SolidHal/btrfld/demos/final_draft.gif

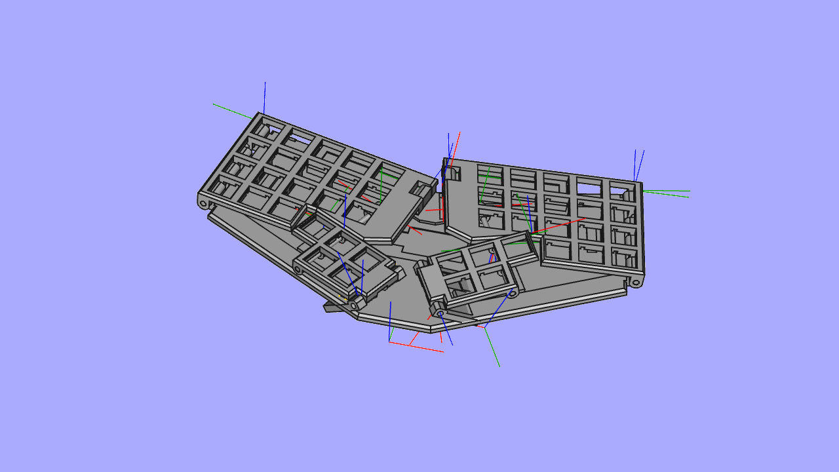
demos/final_draft.gif
