SolidHal/btrfld/demos/first_draft_demo_no_supports.gif

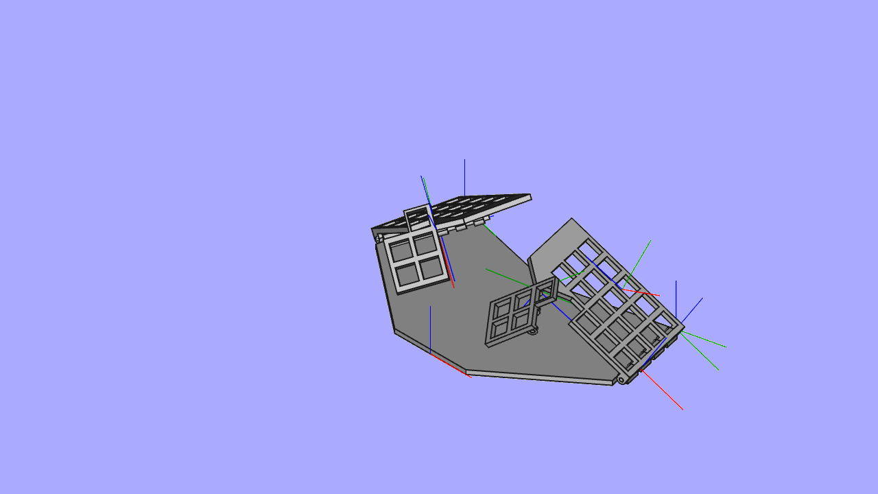
demos/first_draft_demo_no_supports.gif
