SolidHal/btrfld/FinishedPictures/btrfld_folded.jpeg

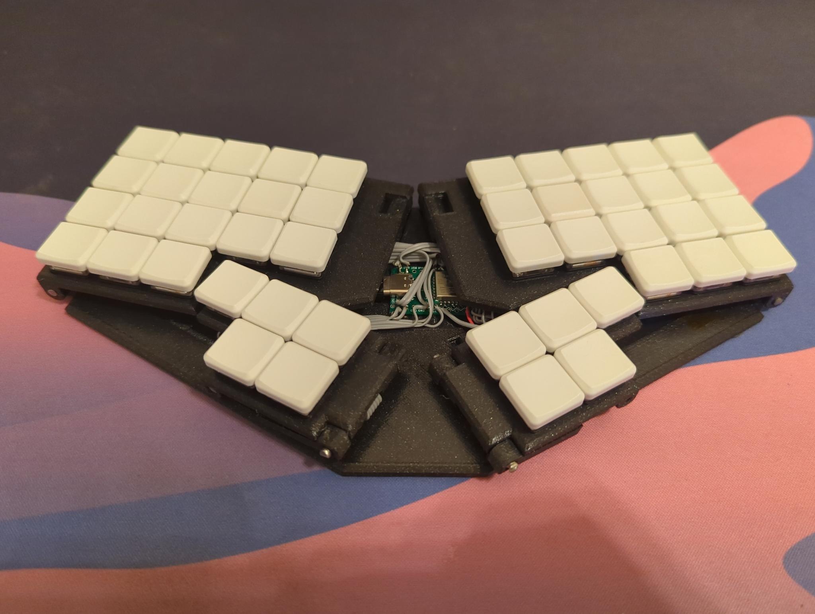
FinishedPictures/btrfld_folded.jpeg
