SolidHal/btrfld/FinishedPictures/btrfld_folded_thickness.jpeg

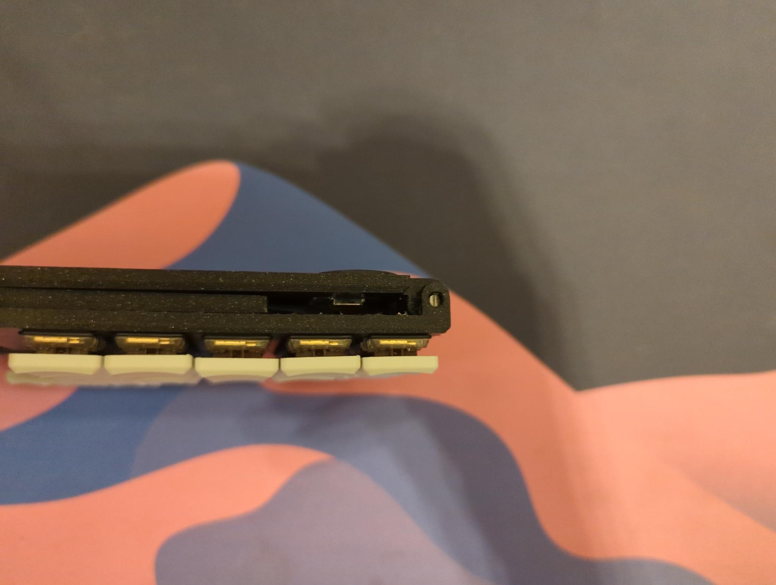
FinishedPictures/btrfld_folded_thickness.jpeg
