SolidHal/btrfld/FinishedPictures/btrfld_front_angle.jpeg

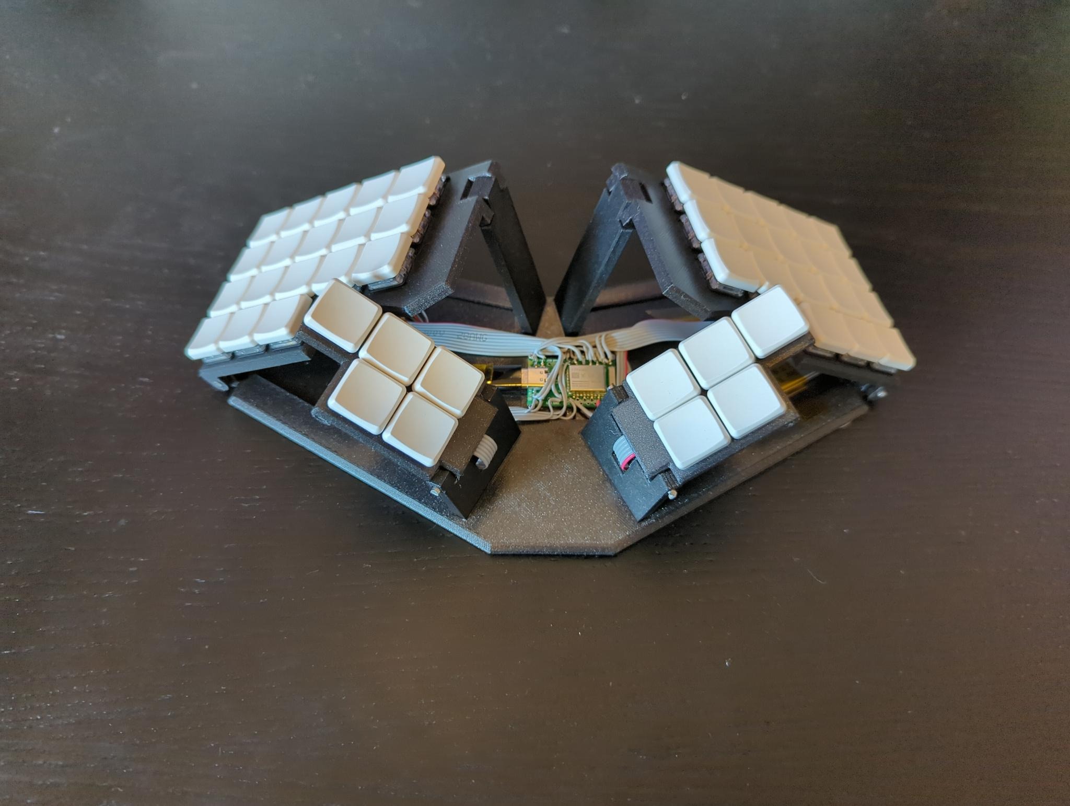
FinishedPictures/btrfld_front_angle.jpeg
