SolidHal/btrfld/FinishedPictures/btrfld_left_front.jpeg

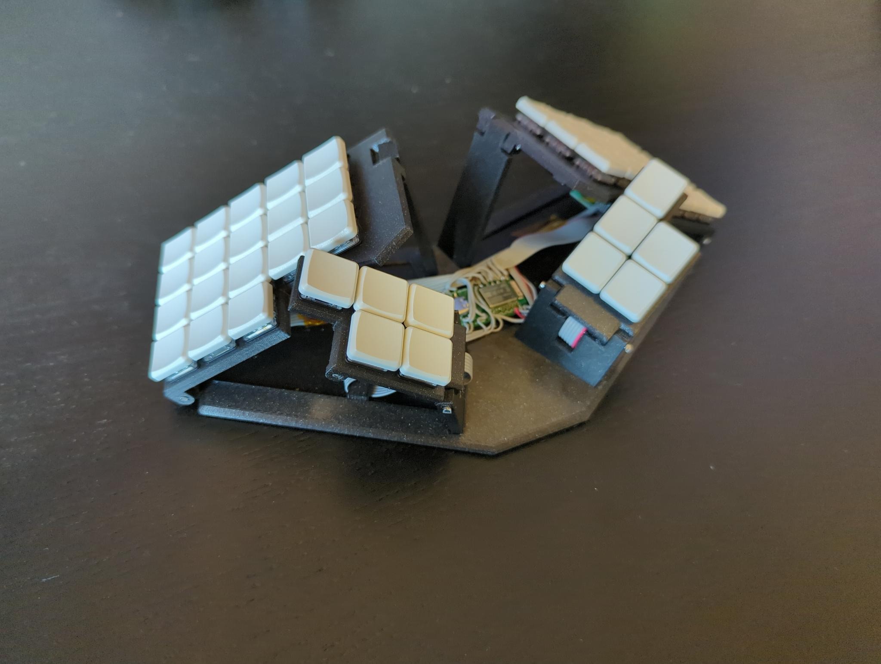
FinishedPictures/btrfld_left_front.jpeg
