SolidHal/btrfld/FinishedPictures/btrfld_right_front.jpeg

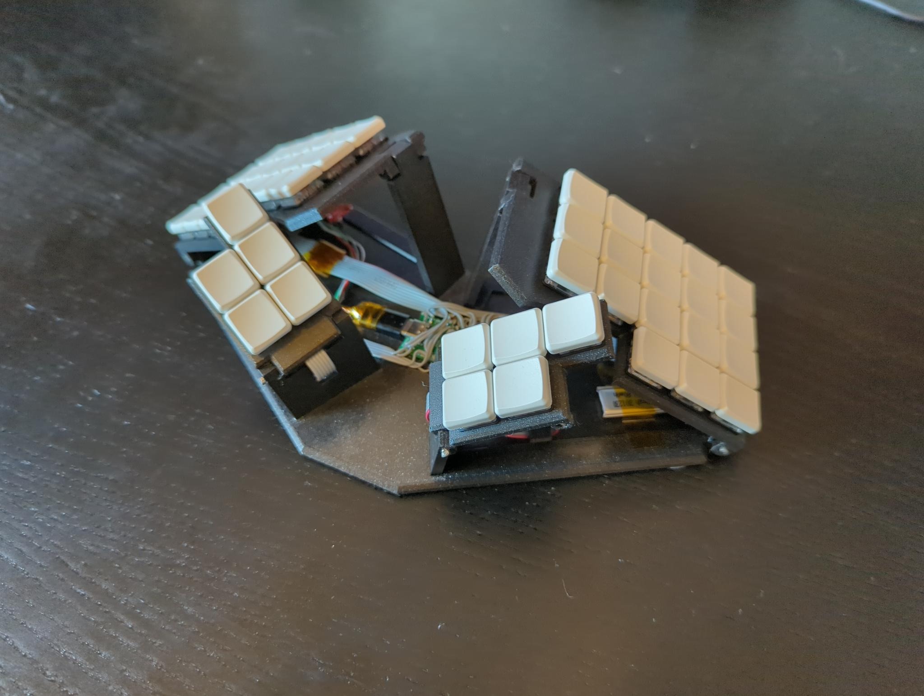
FinishedPictures/btrfld_right_front.jpeg
