SolidHal/btrfld/FinishedPictures/btrfld_top.jpeg

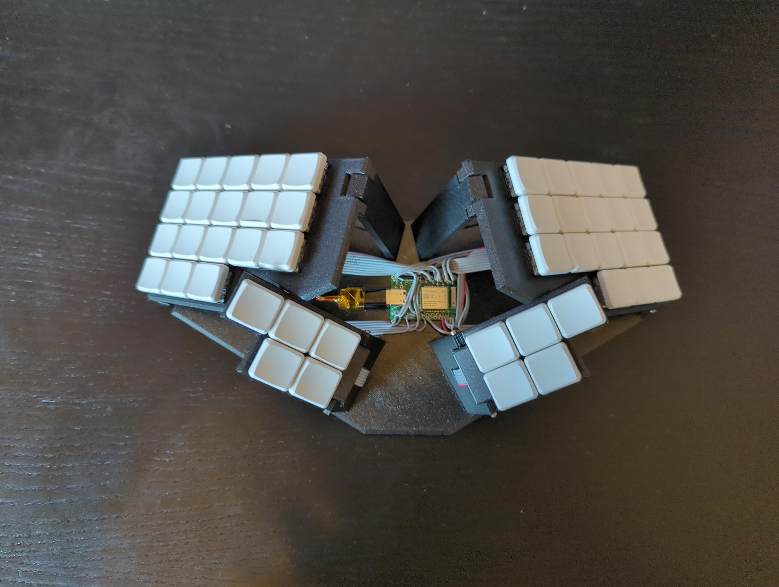
FinishedPictures/btrfld_top.jpeg
