SolidHal/btrfld/FinishedPictures/btrfld_with_btrfly/btrfld_btrfly_front.jpeg

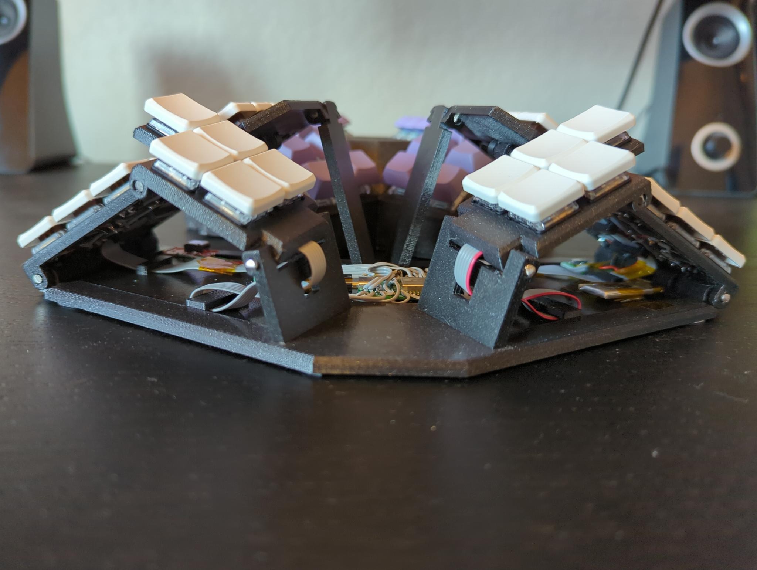
FinishedPictures/btrfld_with_btrfly/btrfld_btrfly_front.jpeg
