SolidHal/btrfld/FinishedPictures/btrfld_with_btrfly/btrfld_btrfly_front_left.jpeg

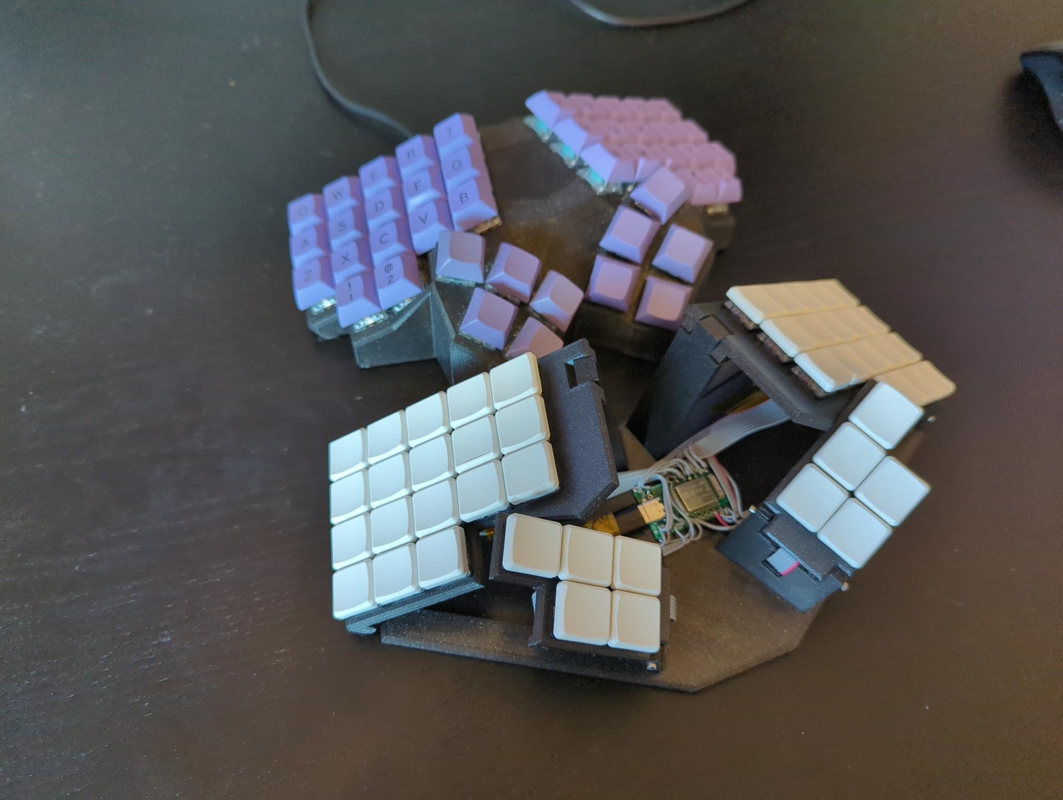
FinishedPictures/btrfld_with_btrfly/btrfld_btrfly_front_left.jpeg
