SolidHal/btrfld/FinishedPictures/btrfld_with_btrfly/btrfld_btrfly_front_top.jpeg

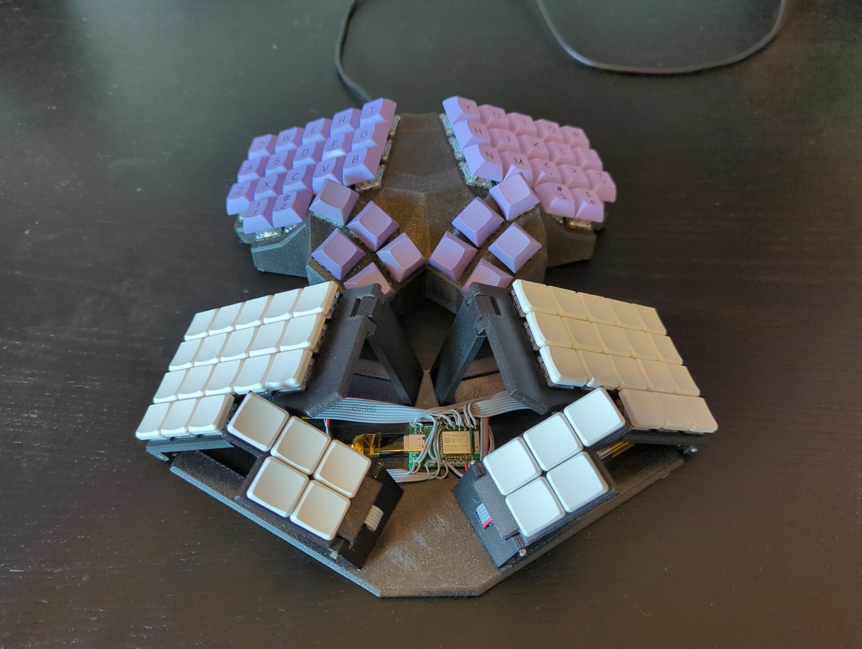
FinishedPictures/btrfld_with_btrfly/btrfld_btrfly_front_top.jpeg
