SolidHal/btrfld/FinishedPictures/btrfld_with_btrfly/btrfld_btrfly_top.jpeg

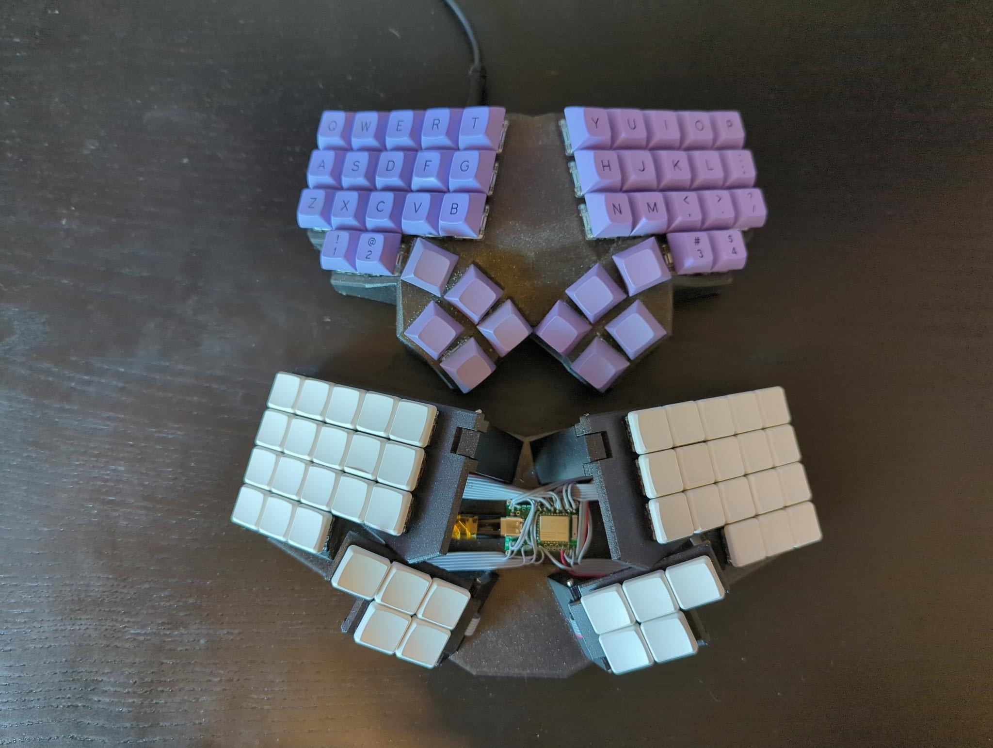
FinishedPictures/btrfld_with_btrfly/btrfld_btrfly_top.jpeg
