SolidHal/btrfld/FinishedPictures/btrfld_with_btrfly/pcb_handwired_btrfly_front_top.jpg

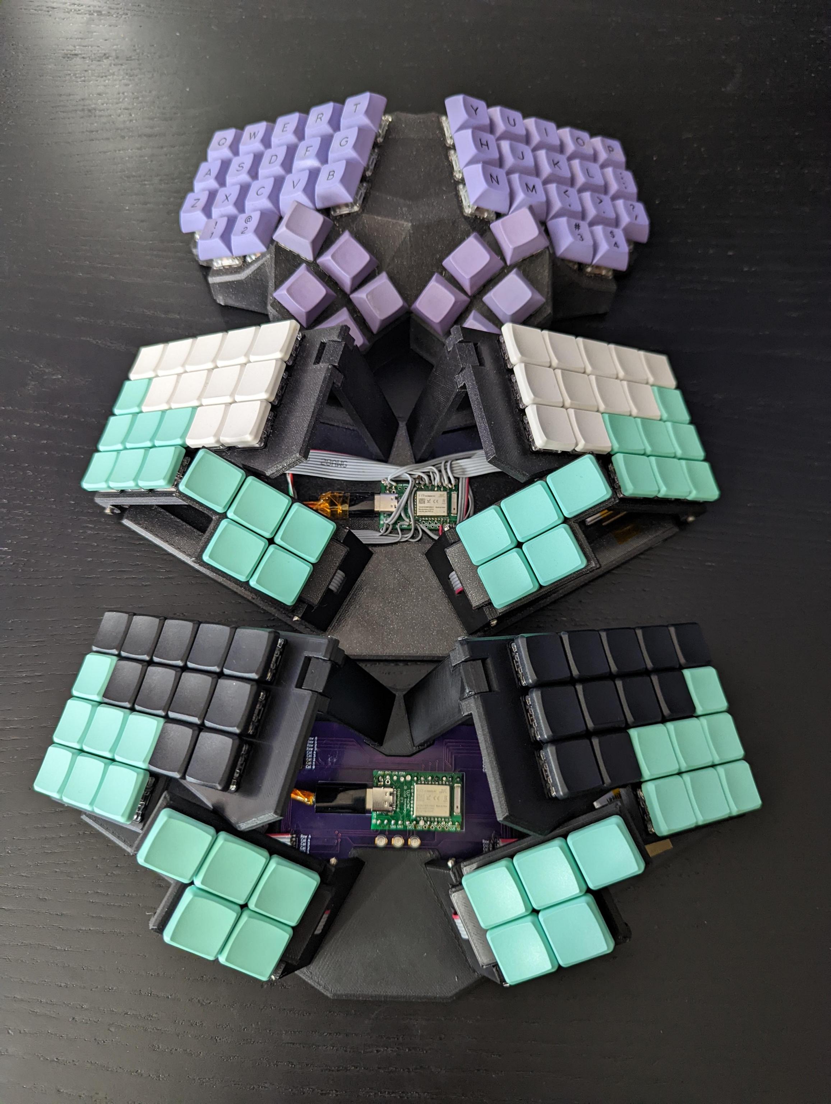
FinishedPictures/btrfld_with_btrfly/pcb_handwired_btrfly_front_top.jpg
