SolidHal/btrfld/FinishedPictures/pcb_handwired_hand_underside.jpg

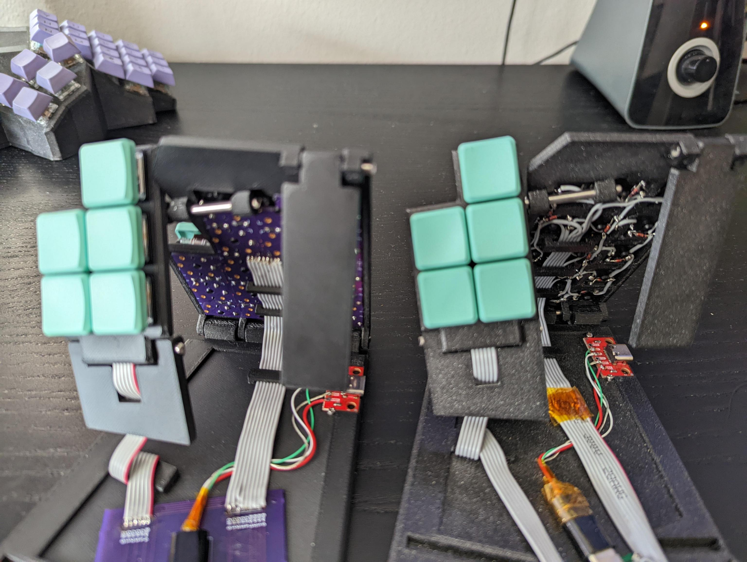
FinishedPictures/pcb_handwired_hand_underside.jpg
