SolidHal/btrfld/FinishedPictures/pcb_handwired_thumb_underside.jpg

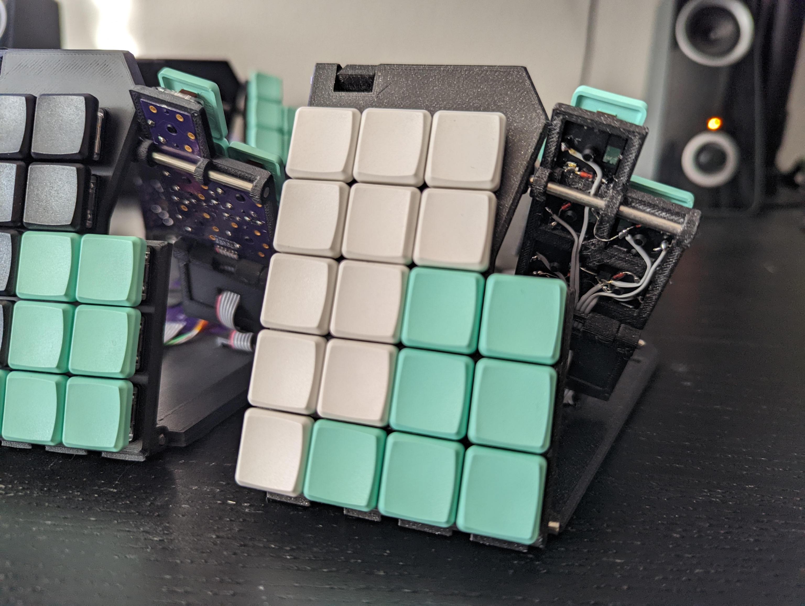
FinishedPictures/pcb_handwired_thumb_underside.jpg
