SolidHal/btrfld/FinishedPictures/ulp_head_on.jpeg

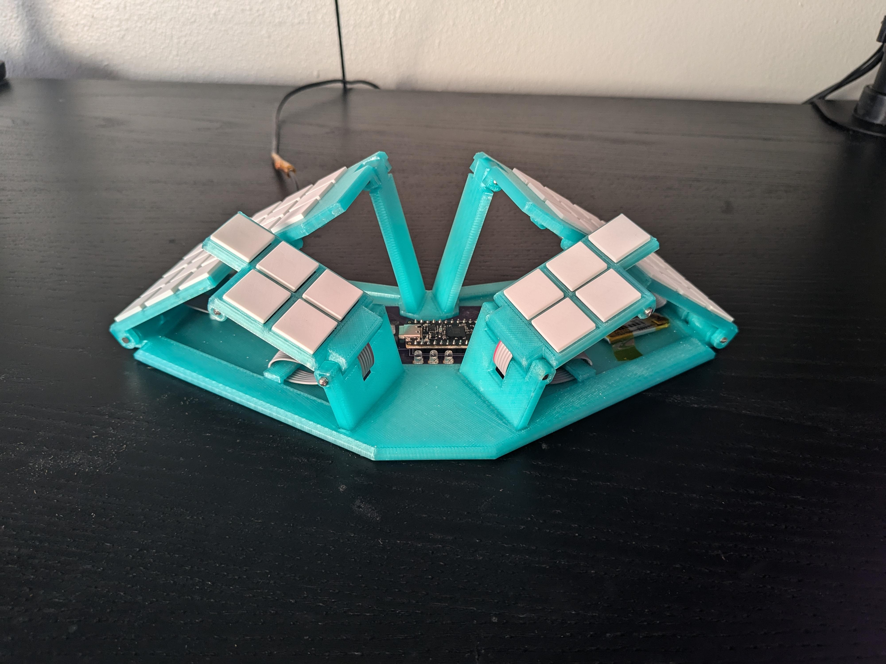
FinishedPictures/ulp_head_on.jpeg
