SolidHal/btrfld/FinishedPictures/ulp_side1.jpeg

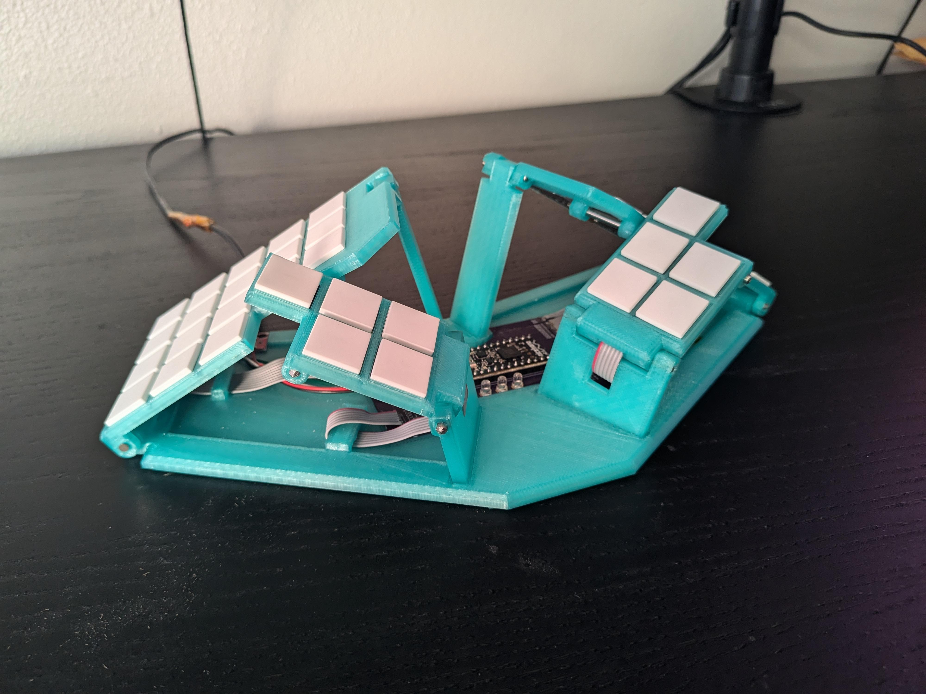
FinishedPictures/ulp_side1.jpeg
