SolidHal/btrfld/FinishedPictures/ulp_side2.jpeg

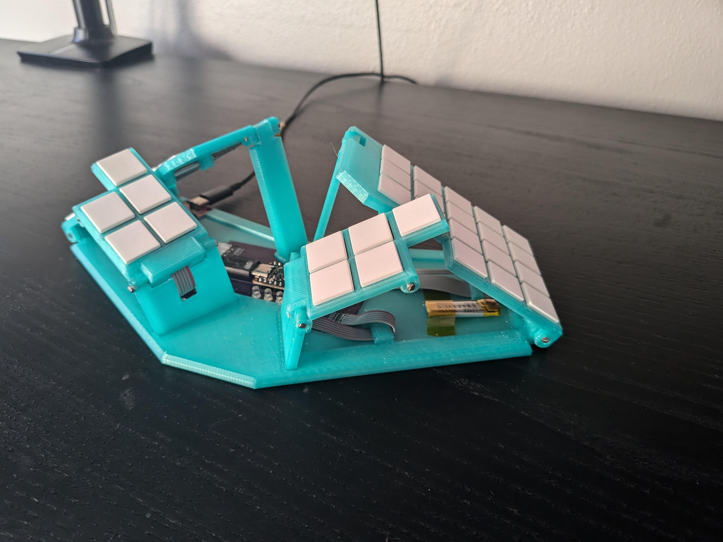
FinishedPictures/ulp_side2.jpeg
