SolidHal/btrfld/FinishedPictures/ulp_with_choc.jpeg

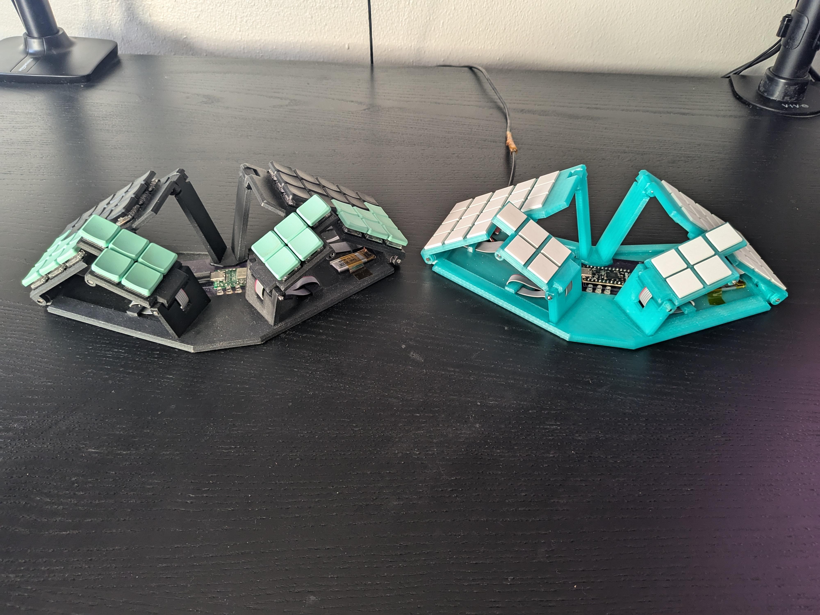
FinishedPictures/ulp_with_choc.jpeg
