SolidHal/btrfld/STLs/btrfld_pcb/test_fit-Baseplate.stl

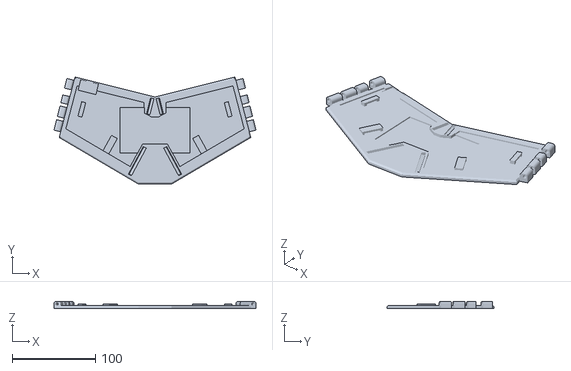
[picture p43: CAD file, 2023-01-31]
STLs/btrfld_pcb/test_fit-Baseplate.stl
242.4 x 128.3 x 9.00
