SolidHal/btrfld/STLs/btrfld_pcb/test_fit-BodyThumRodCap.stl

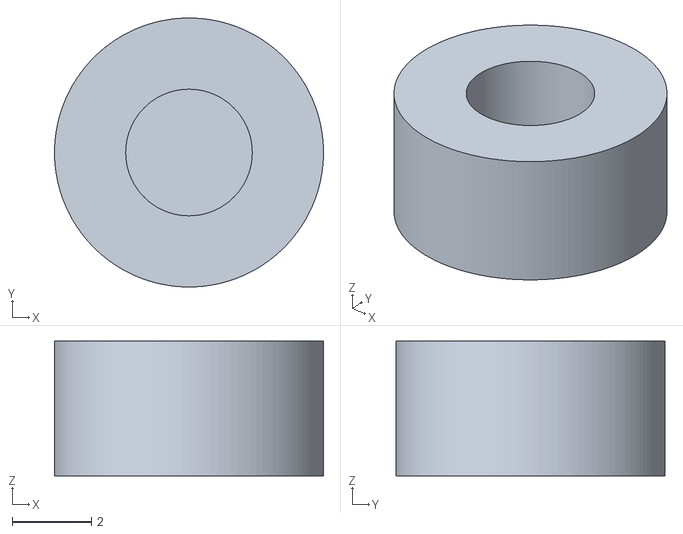
[picture p44: CAD file, 2022-04-27]
STLs/btrfld_pcb/test_fit-BodyThumRodCap.stl
6.80 x 6.80 x 3.40
