SolidHal/btrfld/STLs/btrfld_ulp/btrfld_ulp-BodyBaseSupportRight.stl

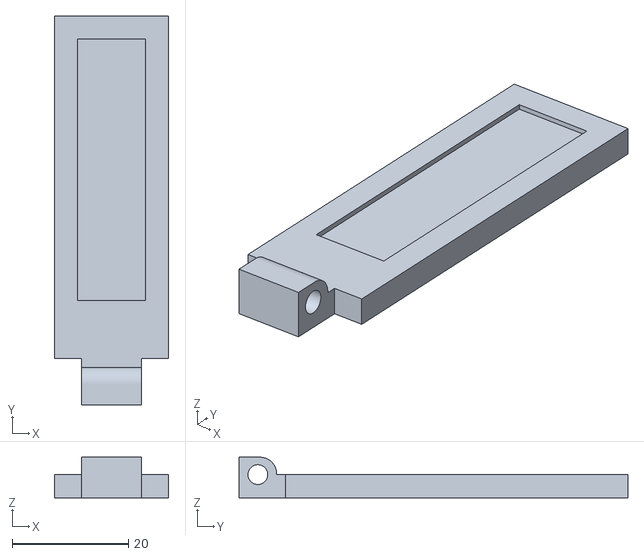
[picture p45: CAD file, 2022-04-27]
STLs/btrfld_ulp/btrfld_ulp-BodyBaseSupportRight.stl
19.7 x 67.0 x 7.00
