SolidHal/btrfld/BuildPictures/HANDWIRED/AllWired/LeftHandWired.jpeg

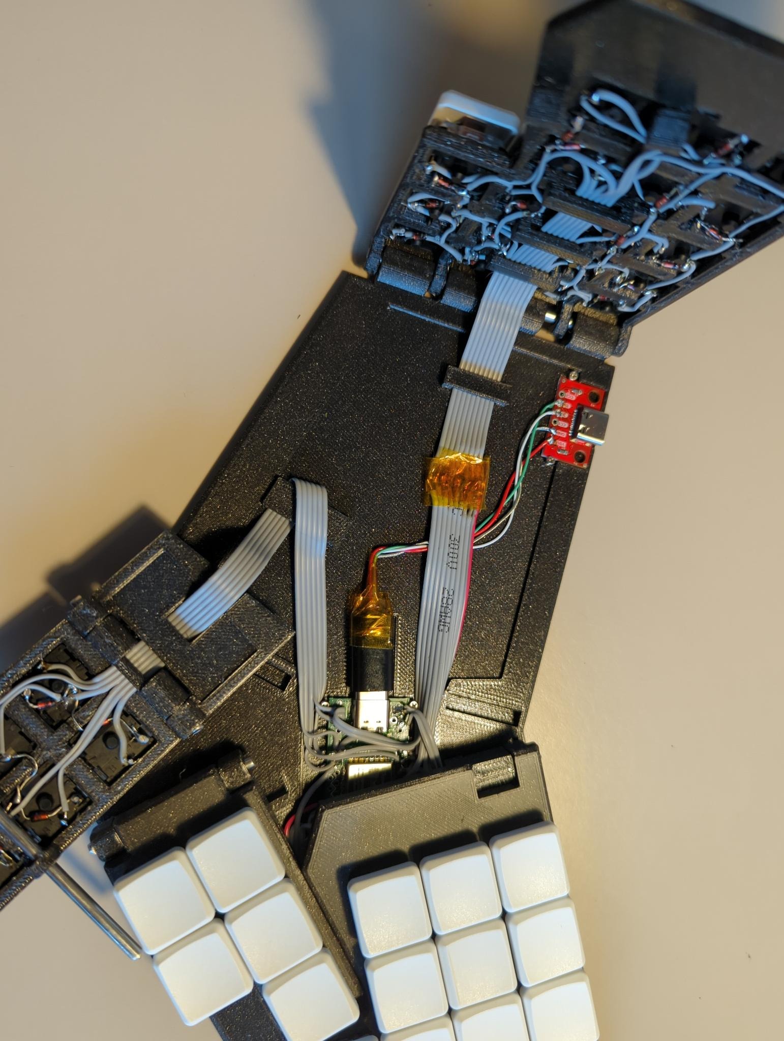
BuildPictures/HANDWIRED/AllWired/LeftHandWired.jpeg
