SolidHal/btrfld/BuildPictures/HANDWIRED/AllWired/LeftSide.jpeg

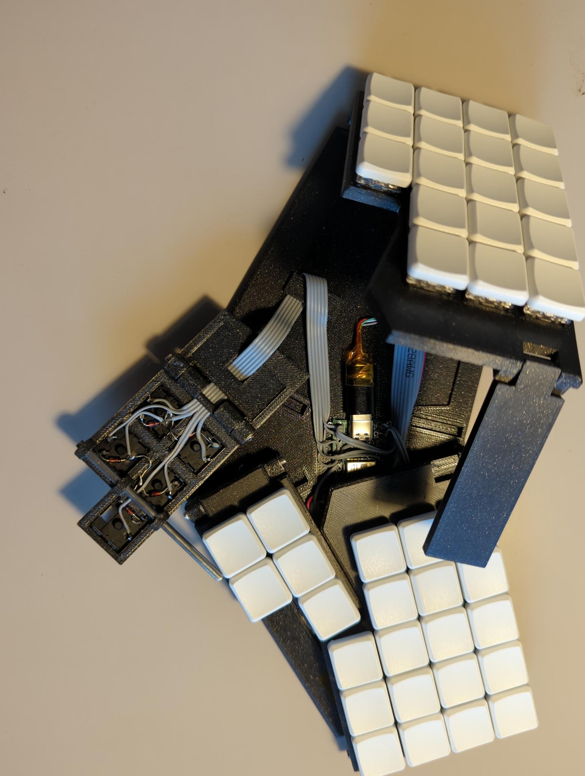
BuildPictures/HANDWIRED/AllWired/LeftSide.jpeg
