SolidHal/btrfld/BuildPictures/HANDWIRED/AllWired/LeftThumbWired.jpeg

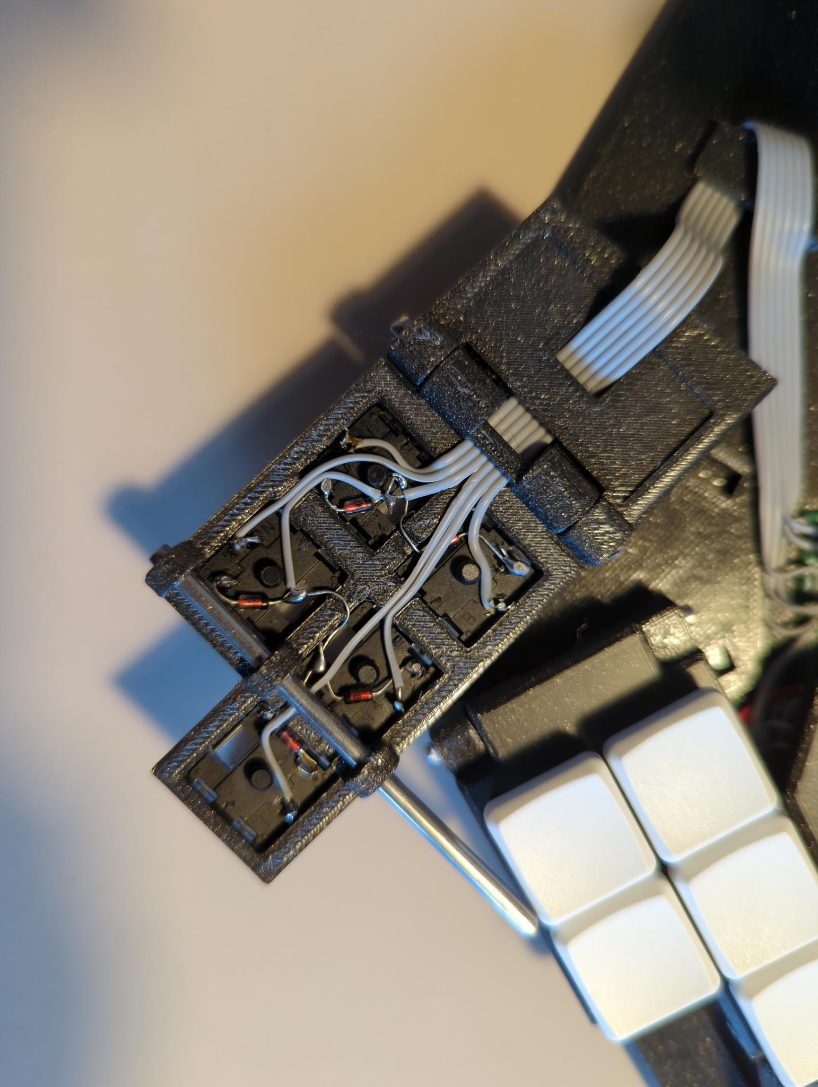
BuildPictures/HANDWIRED/AllWired/LeftThumbWired.jpeg
