SolidHal/btrfld/BuildPictures/HANDWIRED/AllWired/RightHandWiredUnderside.jpeg

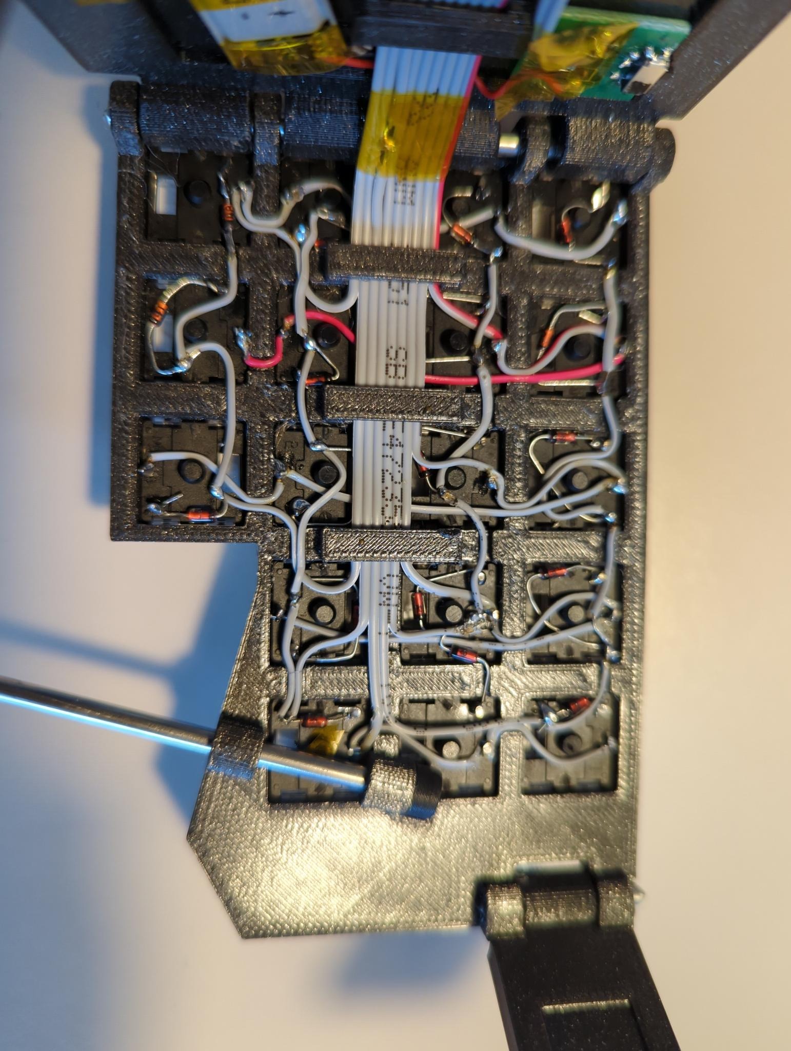
BuildPictures/HANDWIRED/AllWired/RightHandWiredUnderside.jpeg
