SolidHal/btrfld/BuildPictures/HANDWIRED/AllWired/RightSide2.jpeg

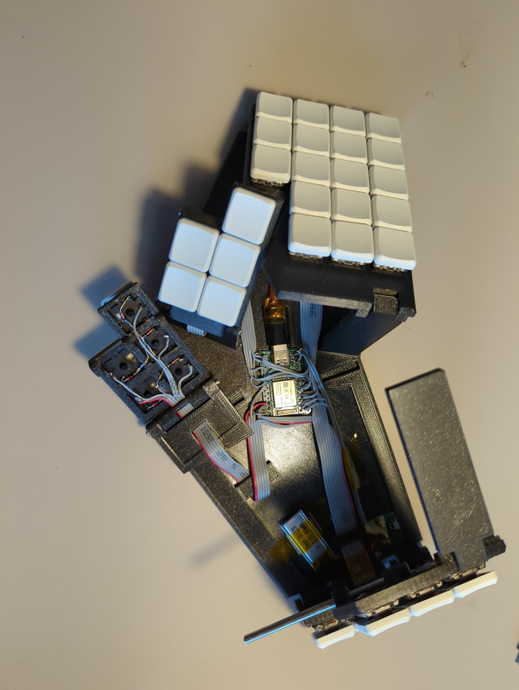
BuildPictures/HANDWIRED/AllWired/RightSide2.jpeg
