SolidHal/btrfld/BuildPictures/HANDWIRED/Assembly/left_hand_unwired.jpeg

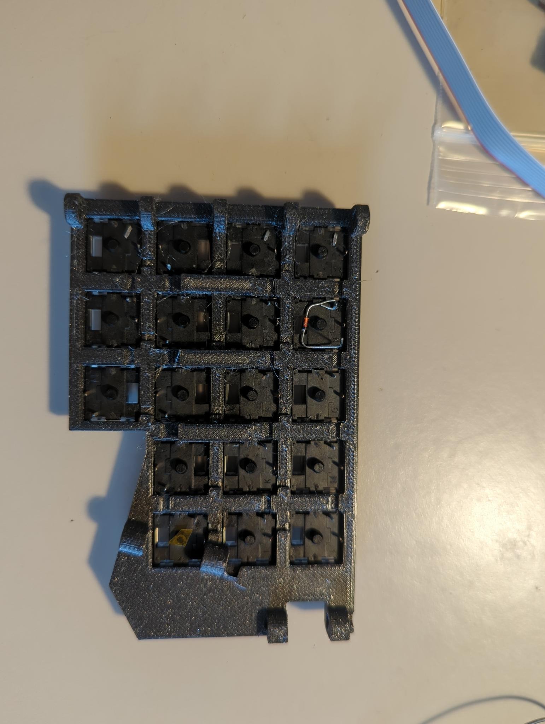
BuildPictures/HANDWIRED/Assembly/left_hand_unwired.jpeg
