SolidHal/btrfld/BuildPictures/HANDWIRED/Assembly/right_hand_wire_planning.jpeg

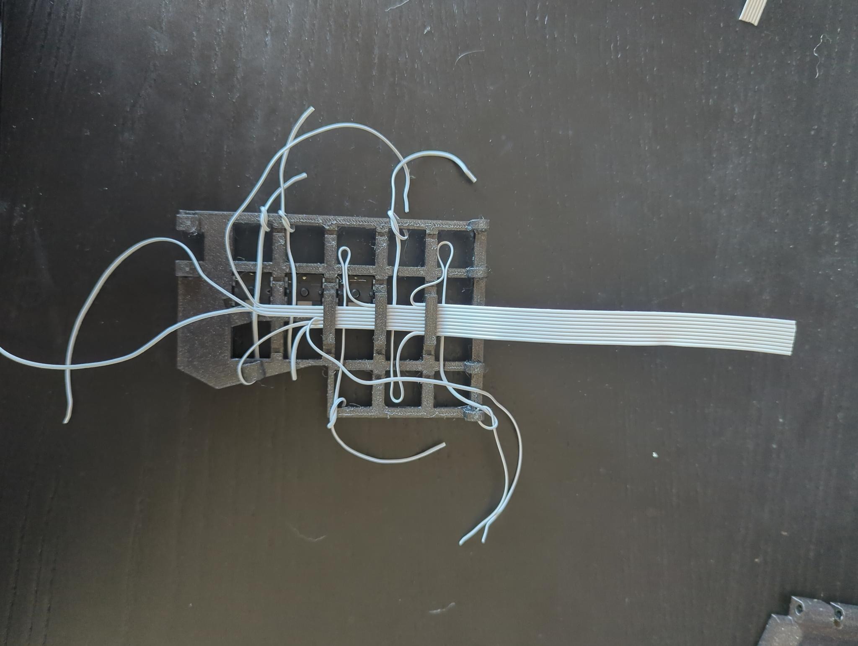
BuildPictures/HANDWIRED/Assembly/right_hand_wire_planning.jpeg
