SolidHal/btrfld/BuildPictures/HANDWIRED/Assembly/thumb_wired.jpeg

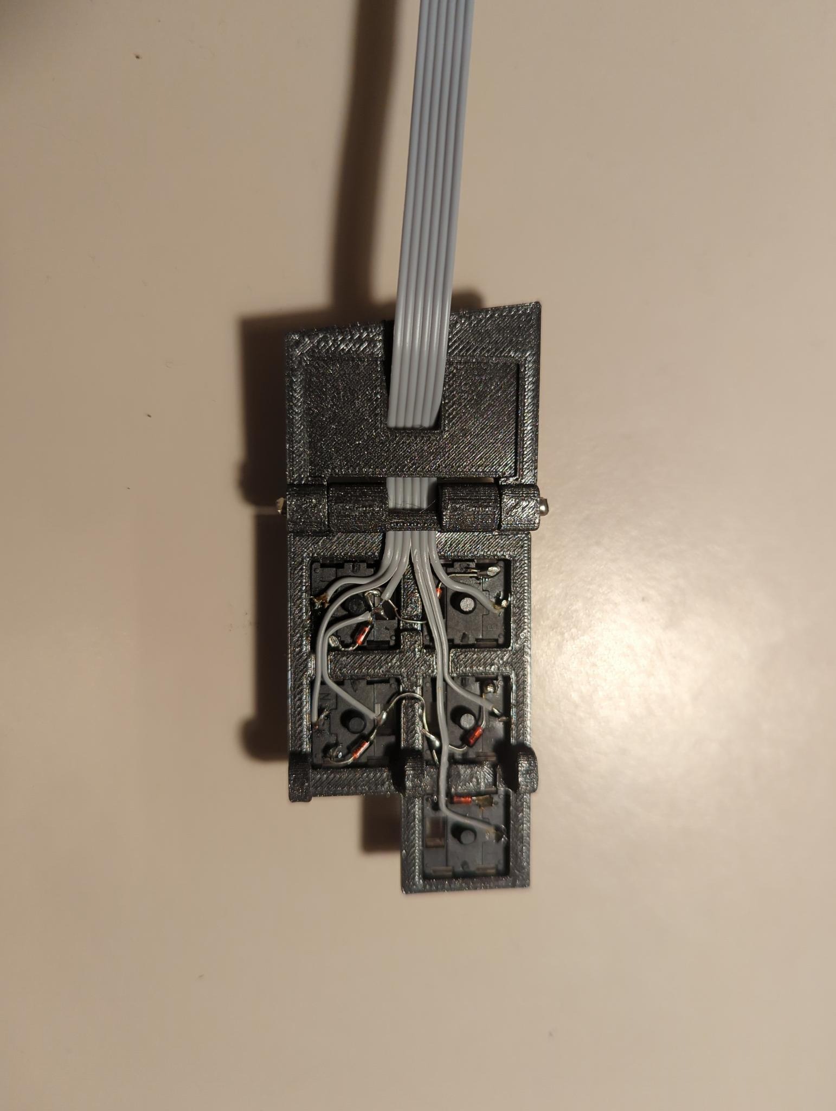
BuildPictures/HANDWIRED/Assembly/thumb_wired.jpeg
