SolidHal/btrfld/BuildPictures/HANDWIRED/Assembly/wiring_the_thumb.jpeg

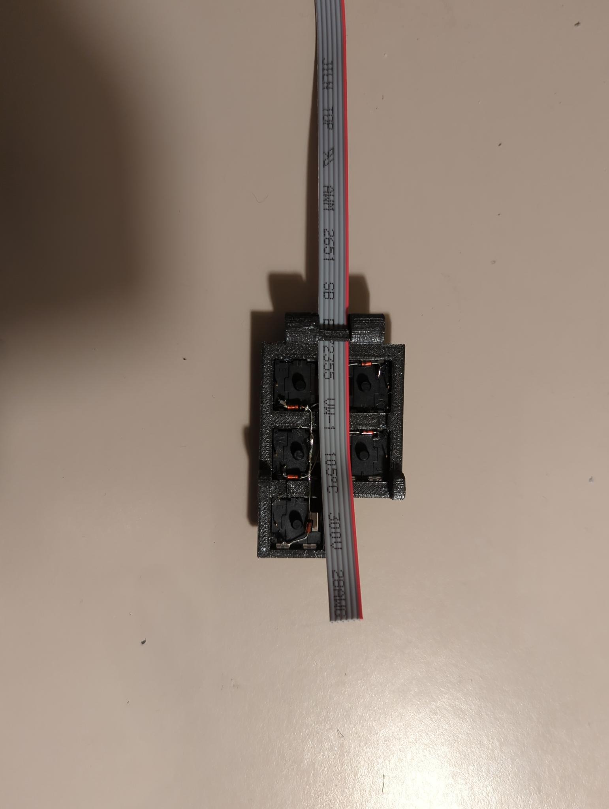
BuildPictures/HANDWIRED/Assembly/wiring_the_thumb.jpeg
