SolidHal/btrfld/BuildPictures/PCB/diodes.jpg

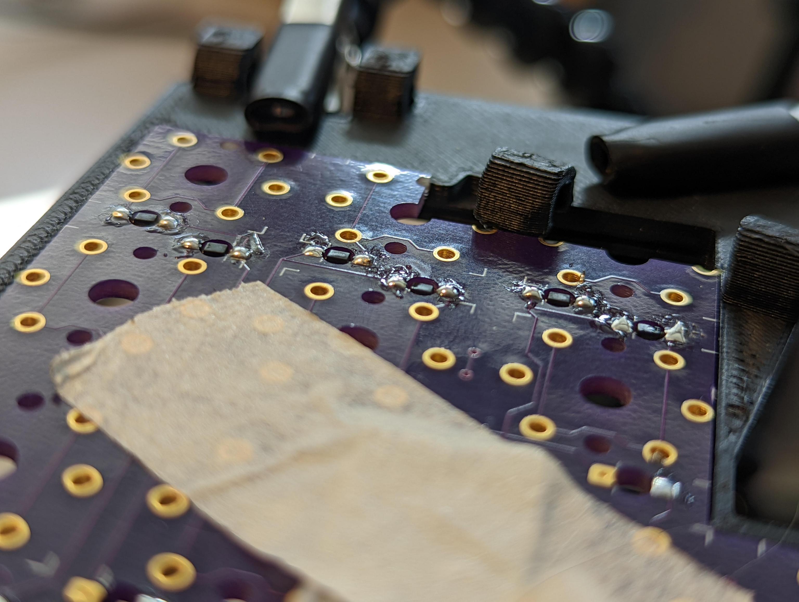
BuildPictures/PCB/diodes.jpg
