SolidHal/btrfld/BuildPictures/PCB/wired_spread.jpg

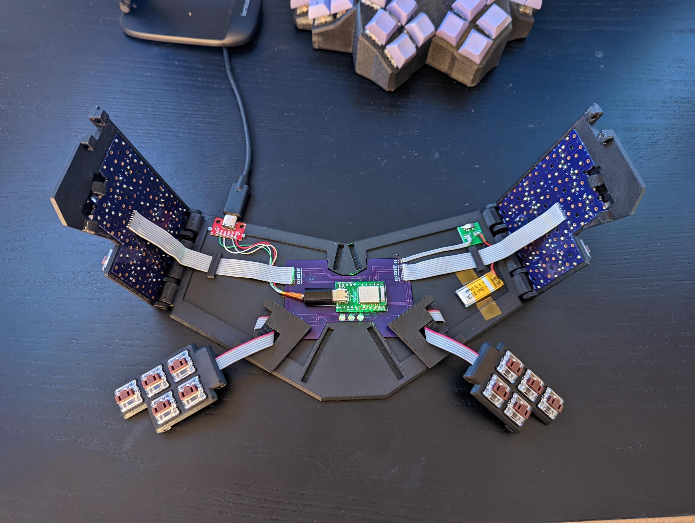
BuildPictures/PCB/wired_spread.jpg
